dekuNukem/gc3ds/nokia_lcd.h

#define LCD_C     LOW
#define LCD_D     HIGH
#define LCD_X     84
#define LCD_Y     48

static const byte ASCII[][5] =
{
 {0x00, 0x00, 0x00, 0x00, 0x00} // 20  
,{0x00, 0x00, 0x5f, 0x00, 0x00} // 21 !
,{0x00, 0x07, 0x00, 0x07, 0x00} // 22 "
,{0x14, 0x7f, 0x14, 0x7f, 0x14} // 23 #
,{0x24, 0x2a, 0x7f, 0x2a, 0x12} // 24 $
,{0x23, 0x13, 0x08, 0x64, 0x62} // 25 %
,{0x36, 0x49, 0x55, 0x22, 0x50} // 26 &
,{0x00, 0x05, 0x03, 0x00, 0x00} // 27 '
,{0x00, 0x1c, 0x22, 0x41, 0x00} // 28 (
,{0x00, 0x41, 0x22, 0x1c, 0x00} // 29 )
,{0x14, 0x08, 0x3e, 0x08, 0x14} // 2a *
,{0x08, 0x08, 0x3e, 0x08, 0x08} // 2b +
,{0x00, 0x50, 0x30, 0x00, 0x00} // 2c ,
,{0x08, 0x08, 0x08, 0x08, 0x08} // 2d -
,{0x00, 0x60, 0x60, 0x00, 0x00} // 2e .
,{0x20, 0x10, 0x08, 0x04, 0x02} // 2f /
,{0x3e, 0x51, 0x49, 0x45, 0x3e} // 30 0
,{0x00, 0x42, 0x7f, 0x40, 0x00} // 31 1
,{0x42, 0x61, 0x51, 0x49, 0x46} // 32 2
,{0x21, 0x41, 0x45, 0x4b, 0x31} // 33 3
,{0x18, 0x14, 0x12, 0x7f, 0x10} // 34 4
,{0x27, 0x45, 0x45, 0x45, 0x39} // 35 5
,{0x3c, 0x4a, 0x49, 0x49, 0x30} // 36 6
,{0x01, 0x71, 0x09, 0x05, 0x03} // 37 7
,{0x36, 0x49, 0x49, 0x49, 0x36} // 38 8
,{0x06, 0x49, 0x49, 0x29, 0x1e} // 39 9
,{0x00, 0x36, 0x36, 0x00, 0x00} // 3a :
,{0x00, 0x56, 0x36, 0x00, 0x00} // 3b ;
,{0x08, 0x14, 0x22, 0x41, 0x00} // 3c <
,{0x14, 0x14, 0x14, 0x14, 0x14} // 3d =
,{0x00, 0x41, 0x22, 0x14, 0x08} // 3e >
,{0x02, 0x01, 0x51, 0x09, 0x06} // 3f ?
,{0x32, 0x49, 0x79, 0x41, 0x3e} // 40 @
,{0x7e, 0x11, 0x11, 0x11, 0x7e} // 41 A
,{0x7f, 0x49, 0x49, 0x49, 0x36} // 42 B
,{0x3e, 0x41, 0x41, 0x41, 0x22} // 43 C
,{0x7f, 0x41, 0x41, 0x22, 0x1c} // 44 D
,{0x7f, 0x49, 0x49, 0x49, 0x41} // 45 E
,{0x7f, 0x09, 0x09, 0x09, 0x01} // 46 F
,{0x3e, 0x41, 0x49, 0x49, 0x7a} // 47 G
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
};

class nokia_lcd
{
private:
	unsigned char reset_pin, chip_enable_pin, dc_pin, sdin_pin, sclk_pin;
public:

	void LcdCharacter(char character)
	{
		LcdWrite(LCD_D, 0x00);
		for(int index = 0; index < 5; index++)
			LcdWrite(LCD_D, ASCII[character - 0x20][index]);
		LcdWrite(LCD_D, 0x00);
	}

	void clear(void)
	{
		for(int index = 0; index < LCD_X * LCD_Y / 8; index++)
			LcdWrite(LCD_D, 0x00);
	}

	nokia_lcd(unsigned char reset, unsigned char ce, unsigned char dc, unsigned char sdin, unsigned char clk, unsigned char contrast)
	{
		reset_pin = reset;
		chip_enable_pin = ce;
		dc_pin = dc;
		sdin_pin = sdin;
		sclk_pin = clk;
		pinMode(chip_enable_pin, OUTPUT);
		pinMode(reset_pin, OUTPUT);
		pinMode(dc_pin, OUTPUT);
		pinMode(sdin_pin, OUTPUT);
		pinMode(sclk_pin, OUTPUT);
		digitalWrite(reset_pin, LOW);
		digitalWrite(reset_pin, HIGH);
		LcdWrite(LCD_C, 0x21);  // LCD Extended Commands.
		LcdWrite(LCD_C, contrast);  // Set LCD Vop (Contrast). 
		LcdWrite(LCD_C, 0x04);  // Set Temp coefficent. //0x04
		LcdWrite(LCD_C, 0x14);  // LCD bias mode 1:48. //0x13
		LcdWrite(LCD_C, 0x0C);  // LCD in normal mode.
		LcdWrite(LCD_C, 0x20);
		LcdWrite(LCD_C, 0x0C);
	}

	void print(char *characters)
	{
		while (*characters)
			LcdCharacter(*characters++);
	}

	void print(long number)
	{
		char buf[13];
		sprintf(buf, "%ld", number);
		print(buf);
	}

	void LcdWrite(byte dc, byte data)
	{
		digitalWrite(dc_pin, dc);
		digitalWrite(chip_enable_pin, LOW);
		shiftOut(sdin_pin, sclk_pin, MSBFIRST, data);
		digitalWrite(chip_enable_pin, HIGH);
	}

	void clear_row(char row)
	{
		gotoXY(0, row);
		print("            ");
	}

	void gotoXY(int x, int y)
	{
		x *= 8;
		LcdWrite(0, 0x80 | x);
		LcdWrite(0, 0x40 | y); 
	}
};
